EorEquis/FlatFlap/Arduino/FlapFlat/functions.ino

void setLight(int val)
{
  if ( val == CALIBRATORREADY)
  {
    digitalWrite(lightPin, relayOn);
    #ifdef DEBUG
      Serial.println("Light on");
    #endif     
  }
  else if ( val == CALIBRATOROFF)
  {
    digitalWrite(lightPin, relayOff);
    #ifdef DEBUG
      Serial.println("Light off");
    #endif              
    
  }                                                                      
}

void setShutter(int val)
{
  
  if ( val == COVEROPEN)
  {
    targetpos = openPos;
  }
  else if ( val == COVERCLOSED)
  {
    targetpos = closedPos;
  }
}
